KasselHand/Lookalike/M-09-Thumb Pawl Spring-1X.STL

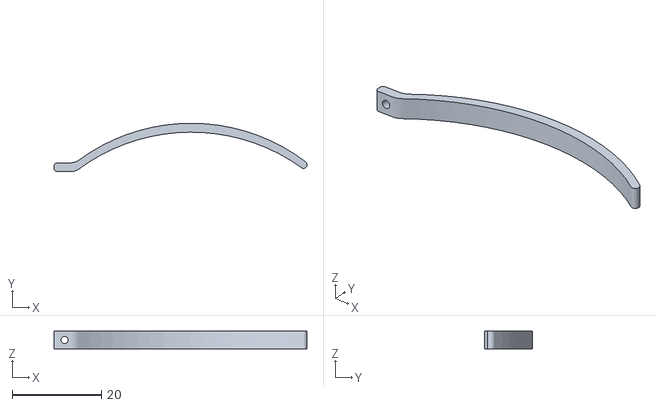
[picture p15: CAD file, 2025-04-07]
M-09-Thumb Pawl Spring-1X.STL
56.8 x 10.9 x 4.00
