KasselHand/Lookalike/M-01-Index Finger V4-1X.STL

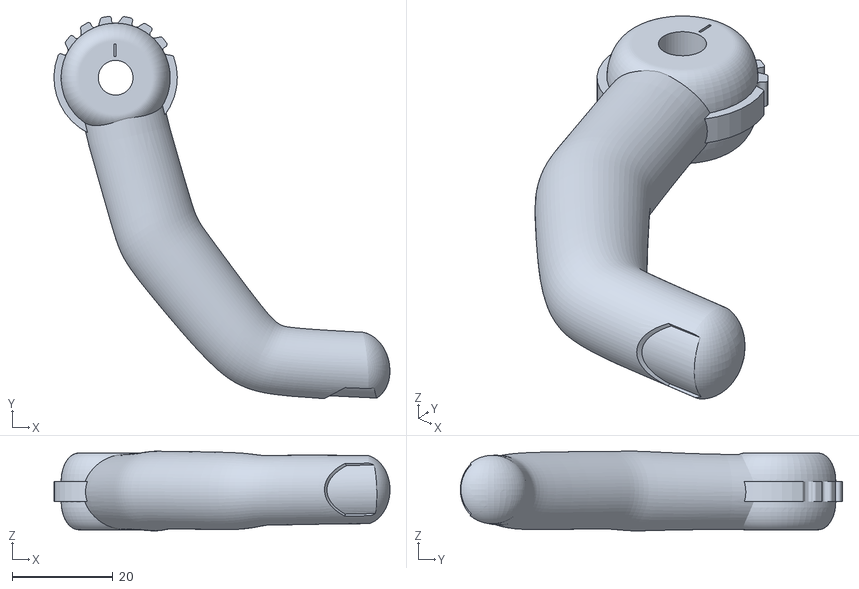
[picture p16: CAD file, 2025-04-07]
M-01-Index Finger V4-1X.STL
66.7 x 75.9 x 15.8
