KasselHand/Lookalike/M-11L Alt-Ratchet Release Paddle-1X.STL

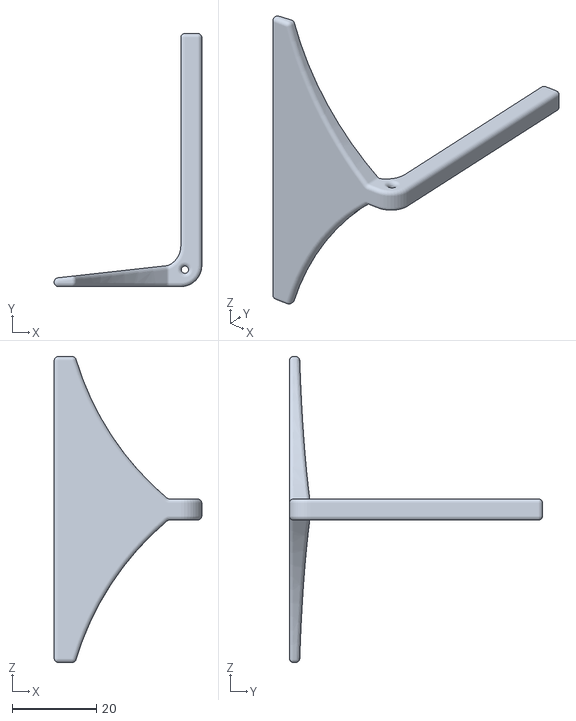
[picture p17: CAD file, 2025-04-07]
M-11L Alt-Ratchet Release Paddle-1X.STL
35.0 x 60.0 x 72.5
