KasselHand/Lookalike/M-05-Thumb V4-1X.STL

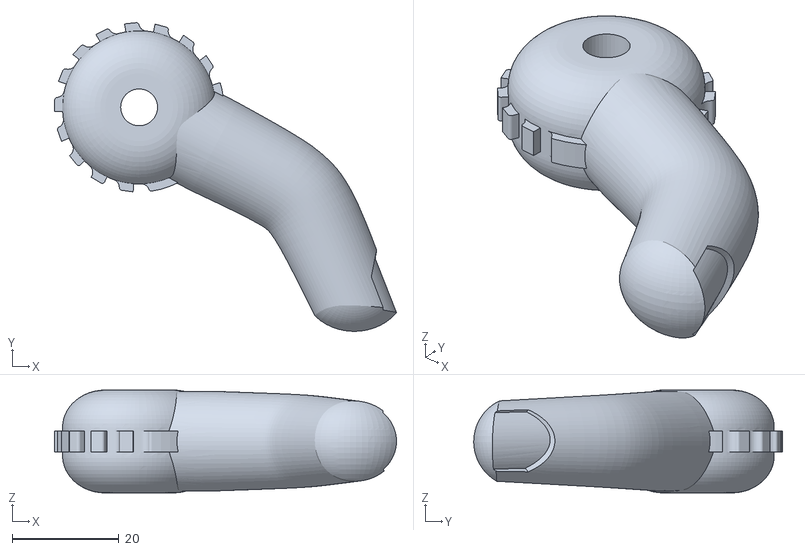
[picture p18: CAD file, 2025-04-07]
M-05-Thumb V4-1X.STL
64.1 x 57.8 x 19.3
