KasselHand/Lookalike/M-08-Thumb Spring-1X.STL

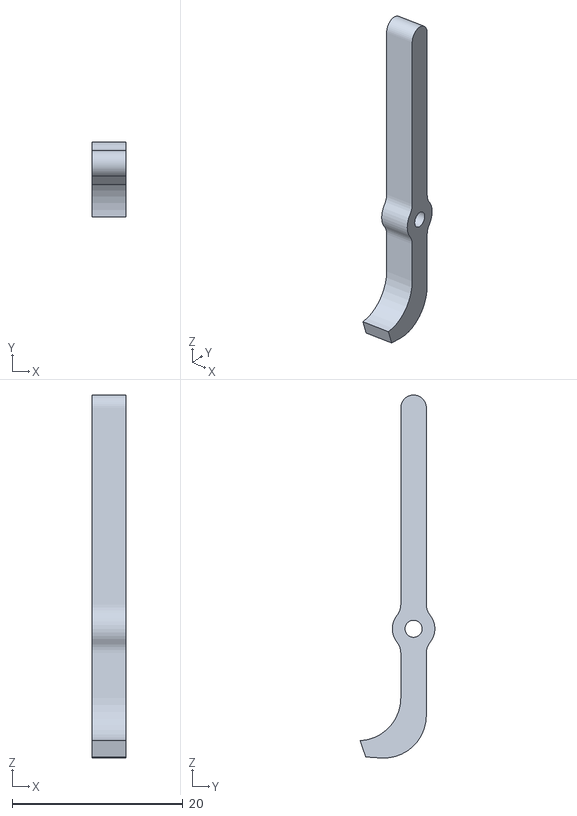
[picture p19: CAD file, 2025-04-07]
M-08-Thumb Spring-1X.STL
4.00 x 8.77 x 42.5
